hlc1209/ecem202a_project/docs/media/oriImg.jpg

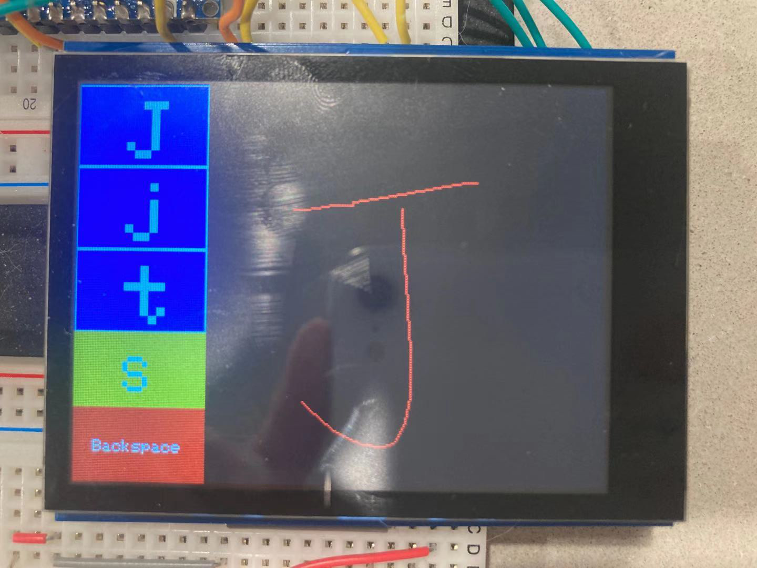
docs/media/oriImg.jpg
