hlc1209/ecem202a_project/docs/media/resizing.PNG

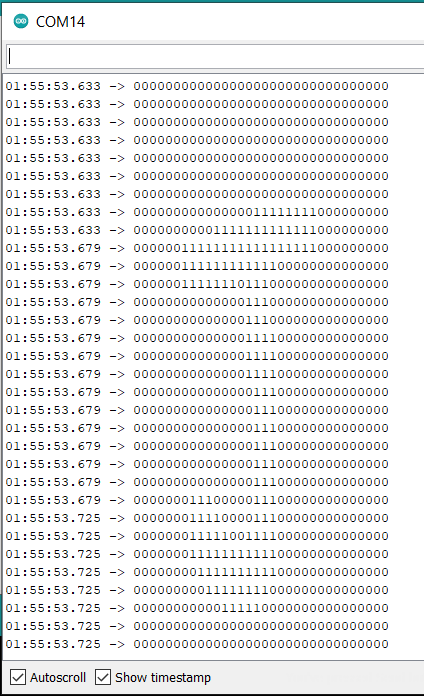
docs/media/resizing.PNG
