hlc1209/ecem202a_project/data/testing_slow_mode.xlsx

Character | Correct Count | Total Count | Accuracy | Total Accuracy
0 | 5 | 5 | 100.00% | 0.9548387097
1 | 5 | 5 | 100.00%
2 | 5 | 5 | 100.00%
3 | 5 | 5 | 100.00%
4 | 4 | 5 | 80.00%
5 | 5 | 5 | 100.00%
6 | 5 | 5 | 100.00%
7 | 5 | 5 | 100.00%
8 | 5 | 5 | 100.00%
9 | 5 | 5 | 100.00%
a | 4 | 5 | 80.00%
b | 4 | 5 | 80.00%
c | 4 | 5 | 80.00%
d | 5 | 5 | 100.00%
e | 5 | 5 | 100.00%
f | 5 | 5 | 100.00%
g | 5 | 5 | 100.00%
h | 5 | 5 | 100.00%
i | 5 | 5 | 100.00%
j | 5 | 5 | 100.00%
k | 4 | 5 | 80.00%
l | 5 | 5 | 100.00%
m | 4 | 5 | 80.00%
n | 5 | 5 | 100.00%
o | 5 | 5 | 100.00%
p | 4 | 5 | 80.00%
q | 5 | 5 | 100.00%
r | 5 | 5 | 100.00%
s | 5 | 5 | 100.00%
t | 5 | 5 | 100.00%
u | 4 | 5 | 80.00%
v | 3 | 5 | 60.00%
w | 5 | 5 | 100.00%
x | 5 | 5 | 100.00%
y | 4 | 5 | 80.00%
z | 4 | 5 | 80.00%
A | 5 | 5 | 100.00%
B | 5 | 5 | 100.00%
C | 5 | 5 | 100.00%
D | 5 | 5 | 100.00%
E | 5 | 5 | 100.00%
F | 5 | 5 | 100.00%
G | 3 | 5 | 60.00%
H | 5 | 5 | 100.00%
I | 5 | 5 | 100.00%
J | 5 | 5 | 100.00%
K | 5 | 5 | 100.00%
L | 5 | 5 | 100.00%
M | 5 | 5 | 100.00%
N | 5 | 5 | 100.00%
O | 5 | 5 | 100.00%
P | 5 | 5 | 100.00%
Q | 5 | 5 | 100.00%
R | 5 | 5 | 100.00%
S | 5 | 5 | 100.00%
T | 5 | 5 | 100.00%
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
