hlc1209/ecem202a_project/software/final_project_arduino_code/model.h

const unsigned char model[] = {
  0x1c, 0x00, 0x00, 0x00, 0x54, 0x46, 0x4c, 0x33, 0x14, 0x00, 0x20, 0x00,
  0x04, 0x00, 0x08, 0x00, 0x0c, 0x00, 0x10, 0x00, 0x14, 0x00, 0x00, 0x00,
  0x18, 0x00, 0x1c, 0x00, 0x14, 0x00, 0x00, 0x00, 0x03, 0x00, 0x00, 0x00,
  0x18, 0x00, 0x00, 0x00, 0x2c, 0x00, 0x00, 0x00, 0x78, 0x01, 0x00, 0x00,
  0x2c, 0x00, 0x00, 0x00, 0x20, 0x01, 0x00, 0x00, 0xa0, 0x00, 0x00, 0x00,
  0x05, 0x00, 0x00, 0x00, 0xe8, 0x0b, 0x00, 0x00, 0xe4, 0x0a, 0x00, 0x00,
  0xd0, 0x08, 0x00, 0x00, 0x2c, 0x03, 0x00, 0x00, 0x84, 0x02, 0x00, 0x00,
  0x01, 0x00, 0x00, 0x00, 0x70, 0x01, 0x00, 0x00, 0x1e, 0x00, 0x00, 0x00,
  0x7c, 0x48, 0x00, 0x00, 0x78, 0x48, 0x00, 0x00, 0x80, 0x47, 0x00, 0x00,
  0xf8, 0x46, 0x00, 0x00, 0x2c, 0x46, 0x00, 0x00, 0x90, 0x45, 0x00, 0x00,
  0x98, 0x43, 0x00, 0x00, 0xc0, 0x42, 0x00, 0x00, 0xa8, 0x3f, 0x00, 0x00,
  0xd0, 0x3e, 0x00, 0x00, 0x18, 0x39, 0x00, 0x00, 0xc0, 0x37, 0x00, 0x00,
  0x88, 0x2d, 0x00, 0x00, 0x30, 0x2c, 0x00, 0x00, 0x38, 0x18, 0x00, 0x00,
  0xe0, 0x15, 0x00, 0x00, 0x68, 0x0d, 0x00, 0x00, 0x04, 0x0c, 0x00, 0x00,
  0x34, 0x48, 0x00, 0x00, 0x30, 0x48, 0x00, 0x00, 0x2c, 0x48, 0x00, 0x00,
  0x28, 0x48, 0x00, 0x00, 0x24, 0x48, 0x00, 0x00, 0x20, 0x48, 0x00, 0x00,
  0x1c, 0x48, 0x00, 0x00, 0x18, 0x48, 0x00, 0x00, 0x14, 0x48, 0x00, 0x00,
  0x10, 0x48, 0x00, 0x00, 0x0c, 0x48, 0x00, 0x00, 0xb4, 0x00, 0x00, 0x00,
  0x01, 0x00, 0x00, 0x00, 0x10, 0x00, 0x00, 0x00, 0x00, 0x00, 0x0a, 0x00,
  0x10, 0x00, 0x0c, 0x00, 0x08, 0x00, 0x04, 0x00, 0x0a, 0x00, 0x00, 0x00,
  0x0c, 0x00, 0x00, 0x00, 0x1c, 0x00, 0x00, 0x00, 0x20, 0x00, 0x00, 0x00,
  0x0f, 0x00, 0x00, 0x00, 0x73, 0x65, 0x72, 0x76, 0x69, 0x6e, 0x67, 0x5f,
  0x64, 0x65, 0x66, 0x61, 0x75, 0x6c, 0x74, 0x00, 0x01, 0x00, 0x00, 0x00,
  0x14, 0x00, 0x00, 0x00, 0x01, 0x00, 0x00, 0x00, 0x24, 0x00, 0x00, 0x00,
  0x08, 0x00, 0x0c, 0x00, 0x08, 0x00, 0x04, 0x00, 0x08, 0x00, 0x00, 0x00,
  0x1b, 0x00, 0x00, 0x00, 0x04, 0x00, 0x00, 0x00, 0x07, 0x00, 0x00, 0x00,
  0x64, 0x65, 0x6e, 0x73, 0x65, 0x5f, 0x33, 0x00, 0x5e, 0xb9, 0xff, 0xff,
  0x04, 0x00, 0x00, 0x00, 0x07, 0x00, 0x00, 0x00, 0x69, 0x6e, 0x70, 0x75,
  0x74, 0x5f, 0x34, 0x00, 0x01, 0x00, 0x00, 0x00, 0x0c, 0x00, 0x00, 0x00,
  0x08, 0x00, 0x0c, 0x00, 0x04, 0x00, 0x08, 0x00, 0x08, 0x00, 0x00, 0x00,
  0x08, 0x00, 0x00, 0x00, 0x1d, 0x00, 0x00, 0x00, 0x13, 0x00, 0x00, 0x00,
  0x6d, 0x69, 0x6e, 0x5f, 0x72, 0x75, 0x6e, 0x74, 0x69, 0x6d, 0x65, 0x5f,
  0x76, 0x65, 0x72, 0x73, 0x69, 0x6f, 0x6e, 0x00, 0xa6, 0xb9, 0xff, 0xff,
  0x04, 0x00, 0x00, 0x00, 0x10, 0x00, 0x00, 0x00, 0x31, 0x2e, 0x31, 0x34,
  0x2e, 0x30, 0x00, 0x00, 0x00, 0x00, 0x00, 0x00, 0x00, 0x00, 0x00, 0x00,
  0x0f, 0x00, 0x00, 0x00, 0x4d, 0x4c, 0x49, 0x52, 0x20, 0x43, 0x6f, 0x6e,
  0x76, 0x65, 0x72, 0x74, 0x65, 0x64, 0x2e, 0x00, 0x00, 0x00, 0x0e, 0x00,
  0x18, 0x00, 0x04, 0x00, 0x08, 0x00, 0x0c, 0x00, 0x10, 0x00, 0x14, 0x00,
  0x0e, 0x00, 0x00, 0x00, 0x14, 0x00, 0x00, 0x00, 0x84, 0x00, 0x00, 0x00,
  0x88, 0x00, 0x00, 0x00, 0x8c, 0x00, 0x00, 0x00, 0xb8, 0x00, 0x00, 0x00,
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
};
